leomachiavello/FundBio2024-2/Hardware/Diseño mecánico/planos_impresion.png

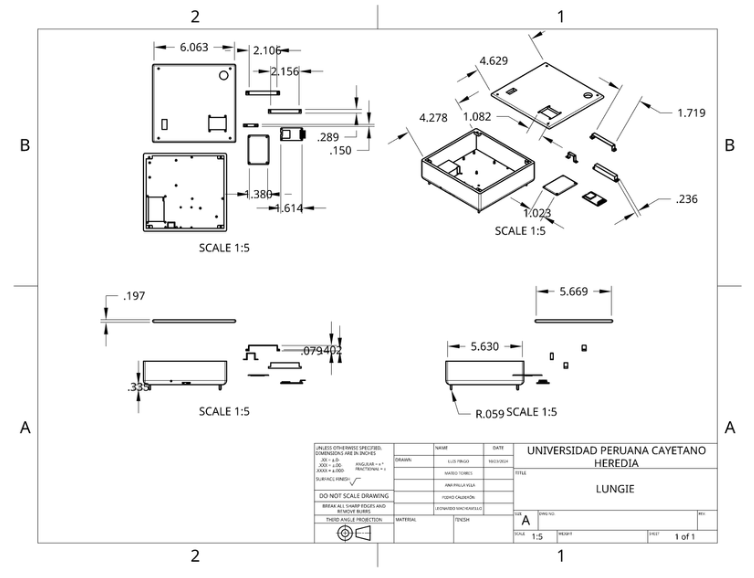
Hardware/Diseño mecánico/planos_impresion.png
