leomachiavello/FundBio2024-2/Imágenes/Espirometría_portátil.png

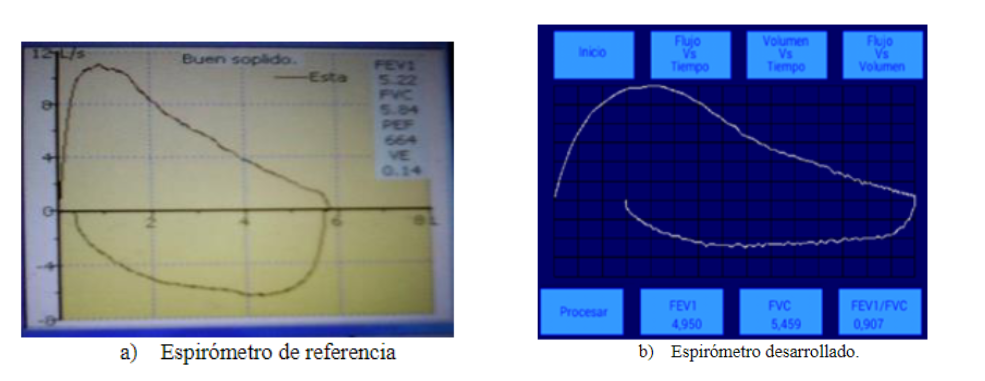
Imágenes/Espirometría_portátil.png
