leomachiavello/FundBio2024-2/Imágenes/espirómetro_asma.png

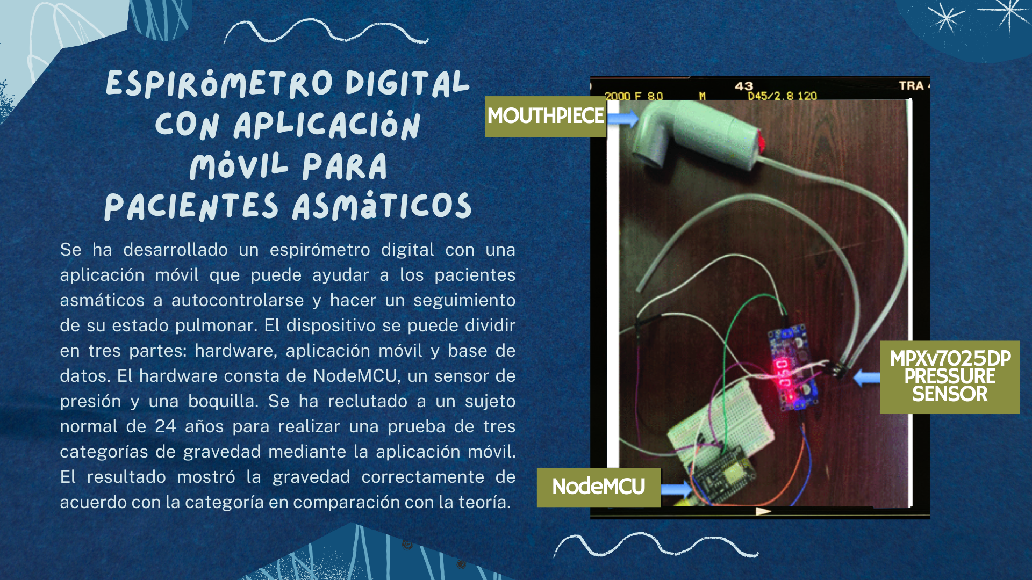
Imágenes/espirómetro_asma.png
