leomachiavello/FundBio2024-2/Imágenes/matriz.png

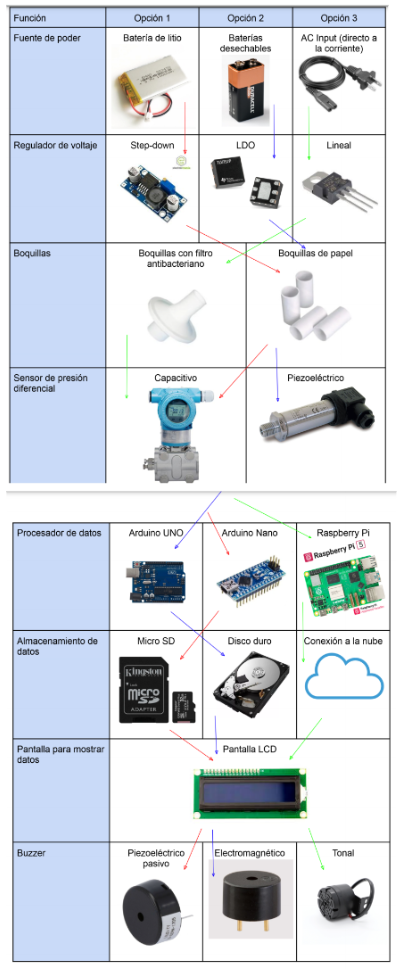
Imágenes/matriz.png
