leomachiavello/FundBio2024-2/Imágenes/matriz_2.png

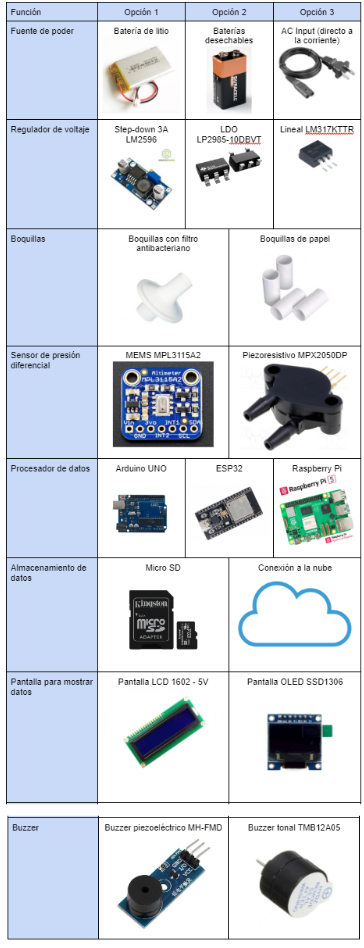
Imágenes/matriz_2.png
