leomachiavello/FundBio2024-2/Imágenes/matriz_3.png

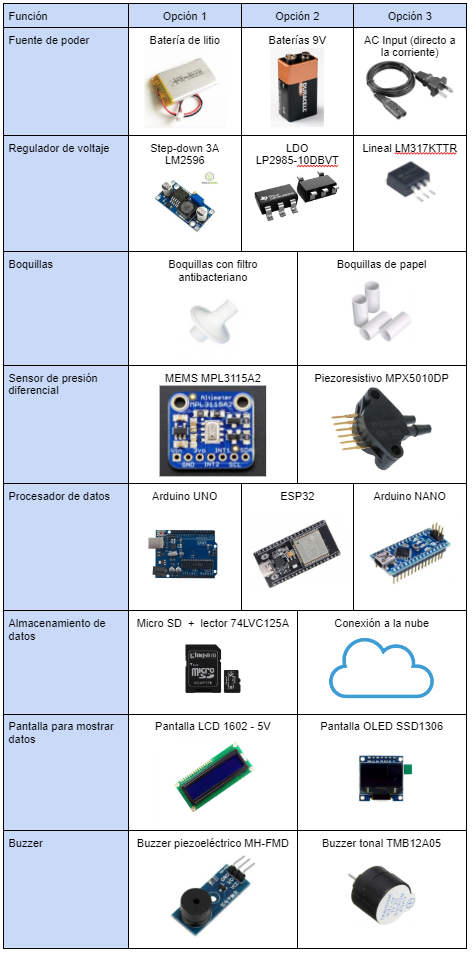
Imágenes/matriz_3.png
