leomachiavello/FundBio2024-2/Imágenes/matriz_4.png

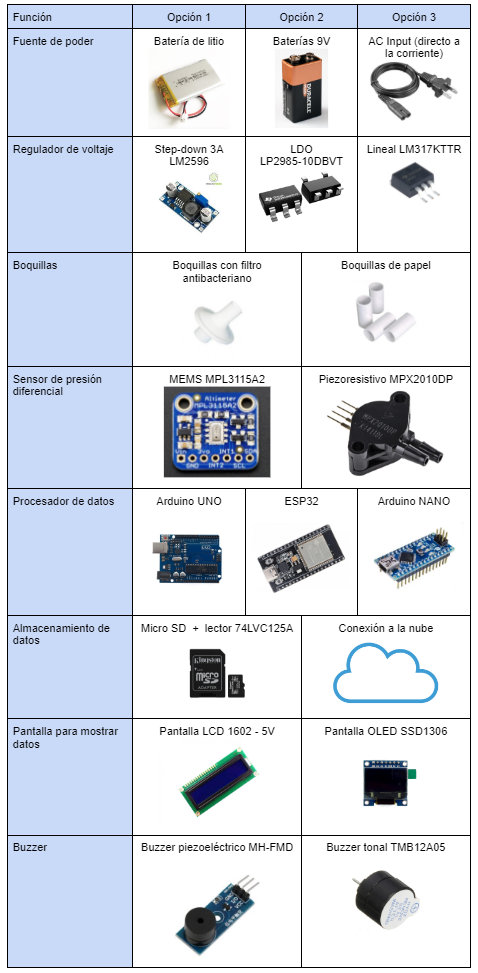
Imágenes/matriz_4.png
