leomachiavello/FundBio2024-2/Imágenes/propuesta_de_solucion.png

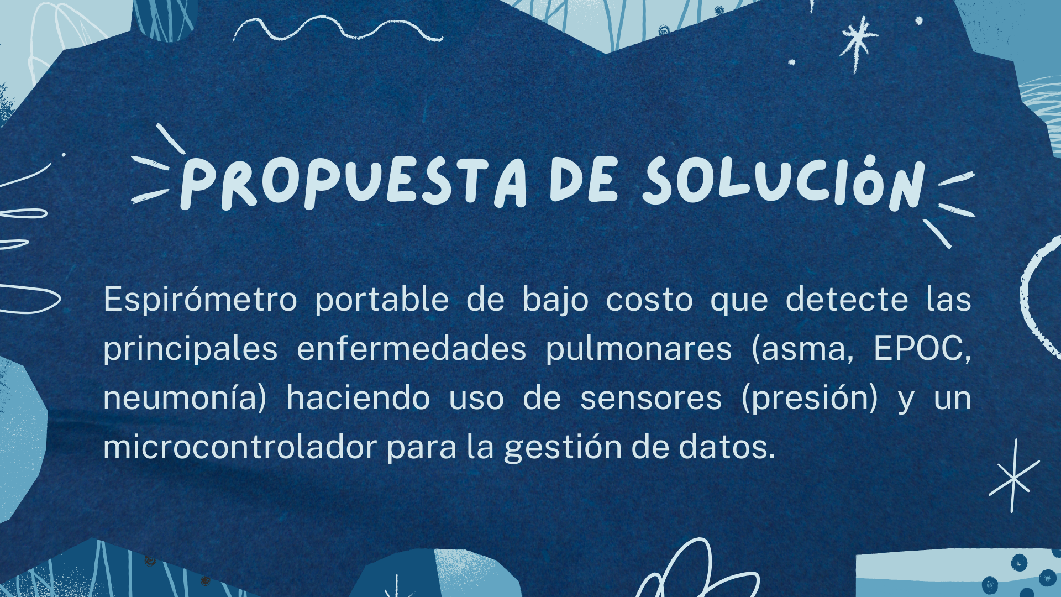
Imágenes/propuesta_de_solucion.png
