leomachiavello/FundBio2024-2/Imágenes/Schematic_FUNBIO_2024-10-08.png

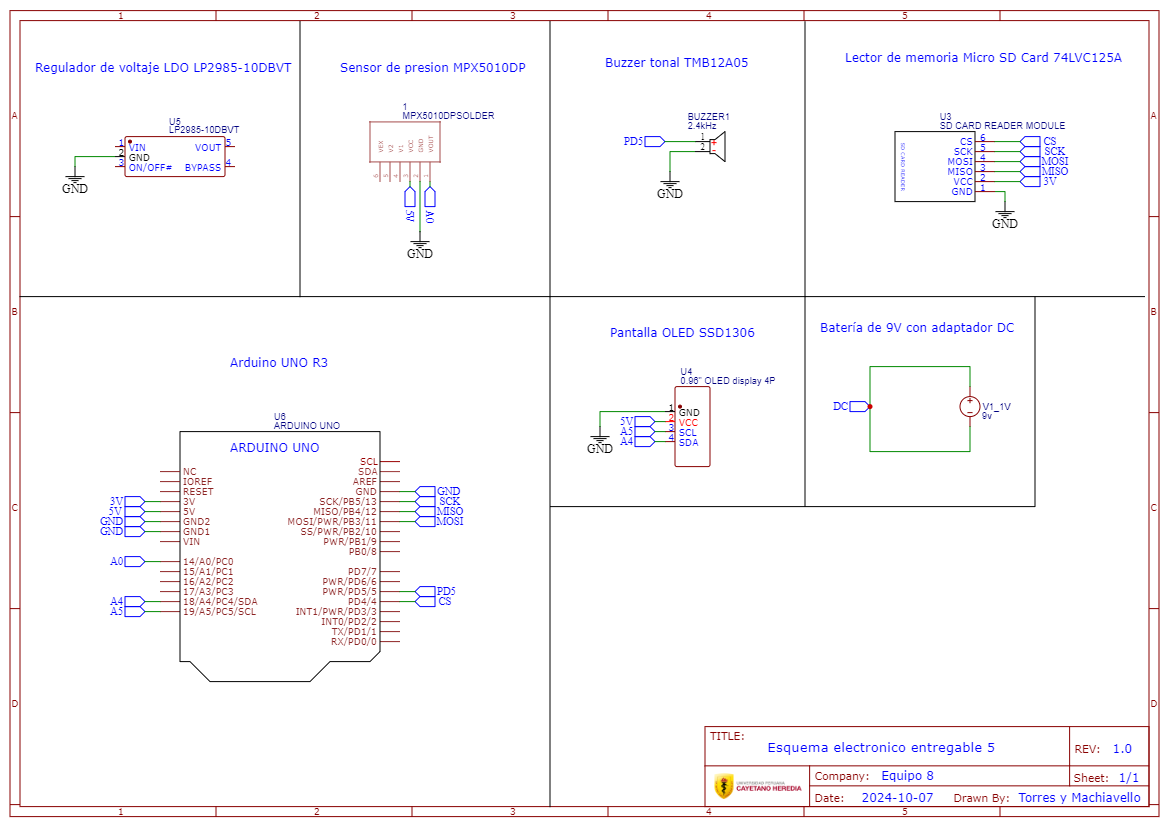
Imágenes/Schematic_FUNBIO_2024-10-08.png
