leomachiavello/FundBio2024-2/Imágenes/tabla_de_valoracion.png

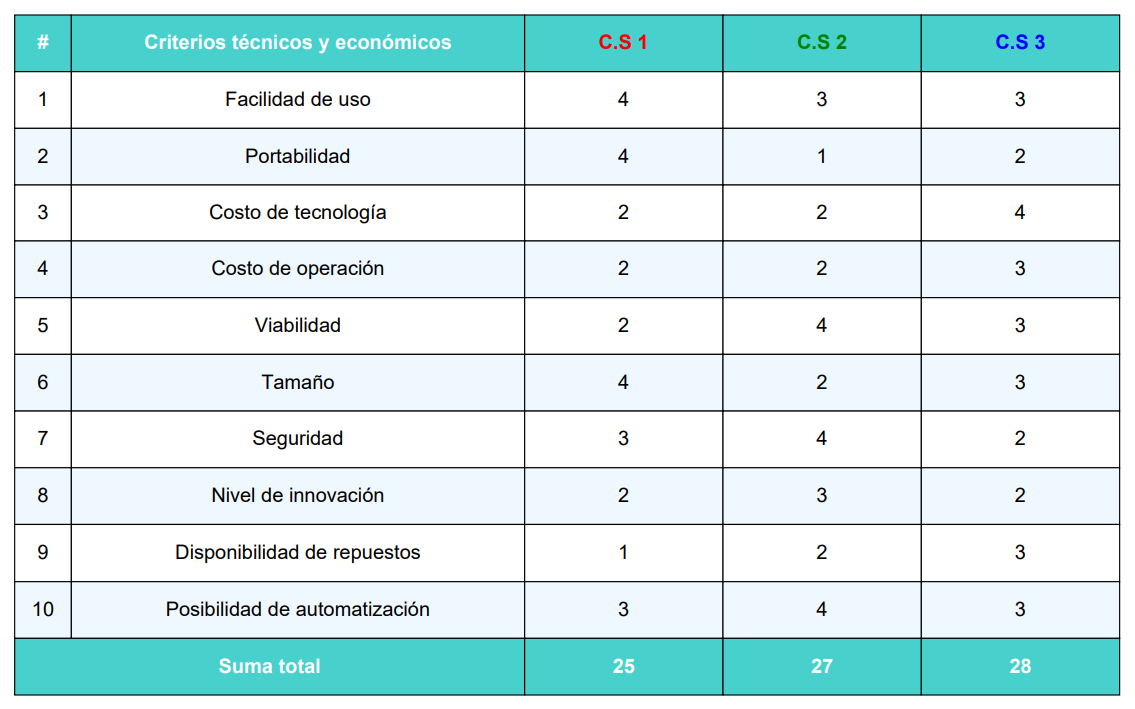
Imágenes/tabla_de_valoracion.png
