leomachiavello/FundBio2024-2/Imágenes/tabla_de_valoracion_2.png

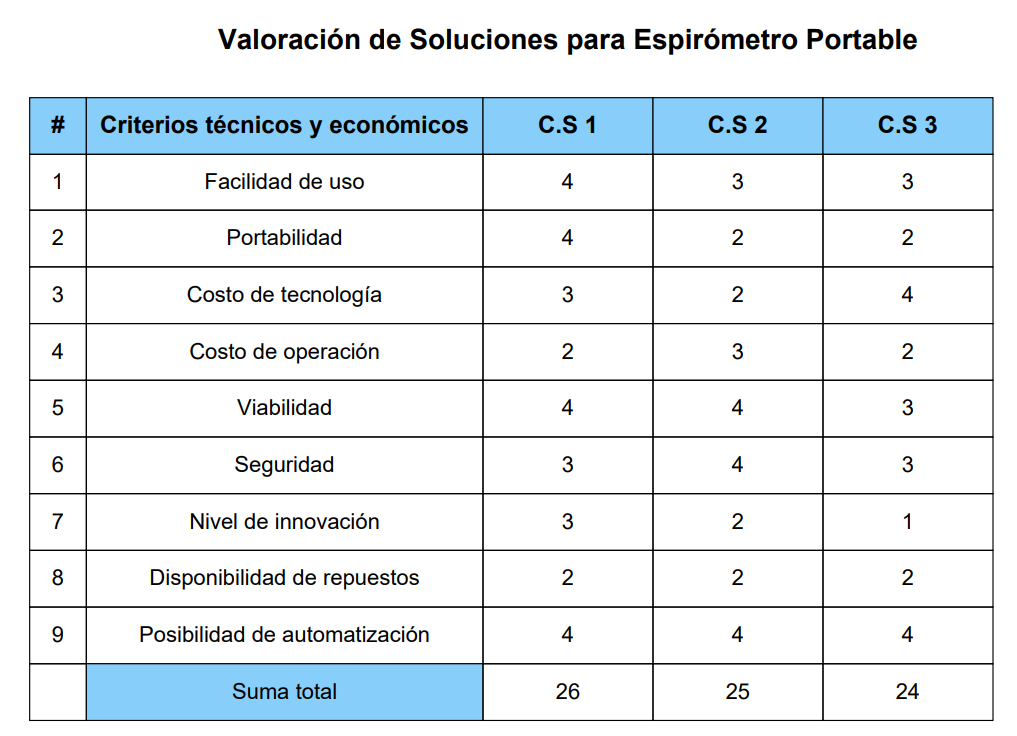
Imágenes/tabla_de_valoracion_2.png
