leomachiavello/FundBio2024-2/Imágenes/Tabla_requerimientos2.png

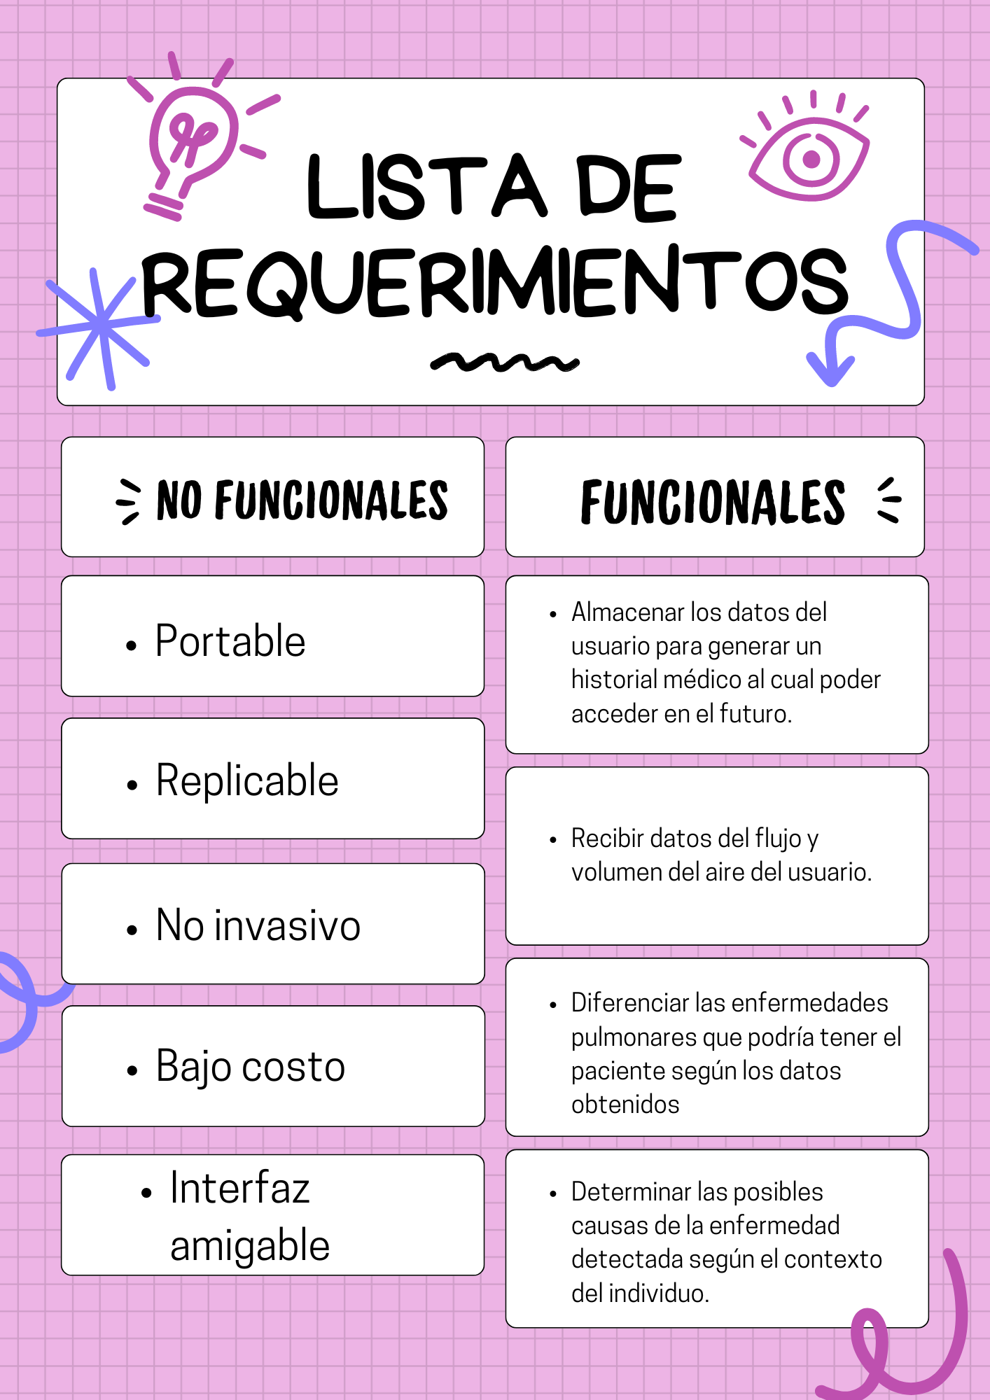
Imágenes/Tabla_requerimientos2.png
