leomachiavello/FundBio2024-2/Hardware/Diseño mecánico/Ensamblaje/Ensamblado_base.png

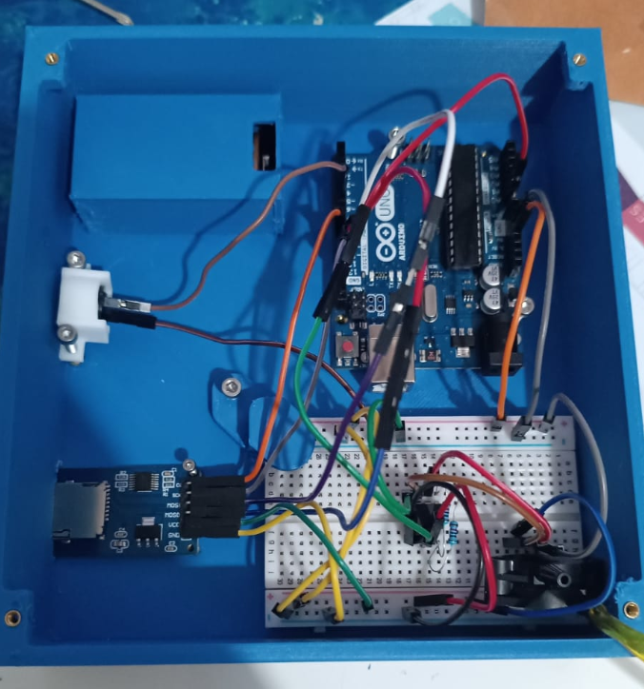
Hardware/Diseño mecánico/Ensamblaje/Ensamblado_base.png
