leomachiavello/FundBio2024-2/Hardware/Diseño mecánico/Ensamblaje/Ensamblado_tapa.png

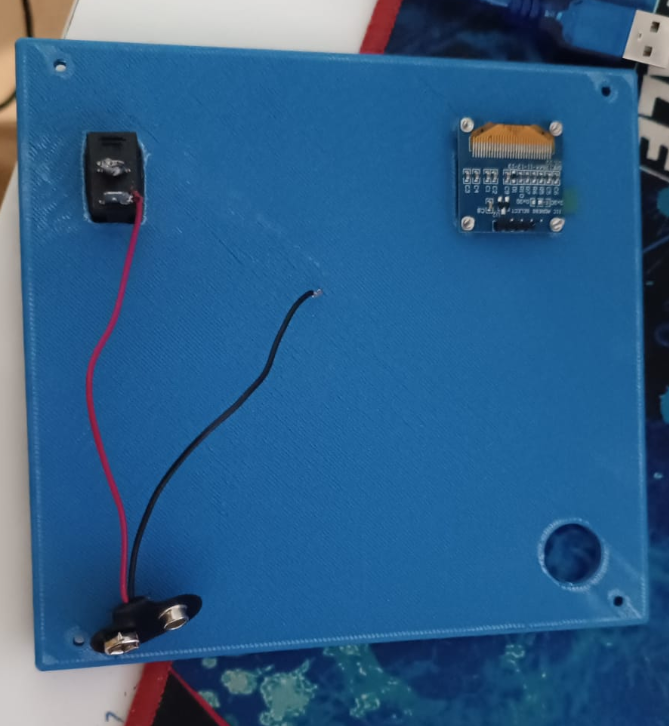
Hardware/Diseño mecánico/Ensamblaje/Ensamblado_tapa.png
