leomachiavello/FundBio2024-2/Hardware/Diseño mecánico/Planos borrador/Plano Soporte Buzzer.pdf

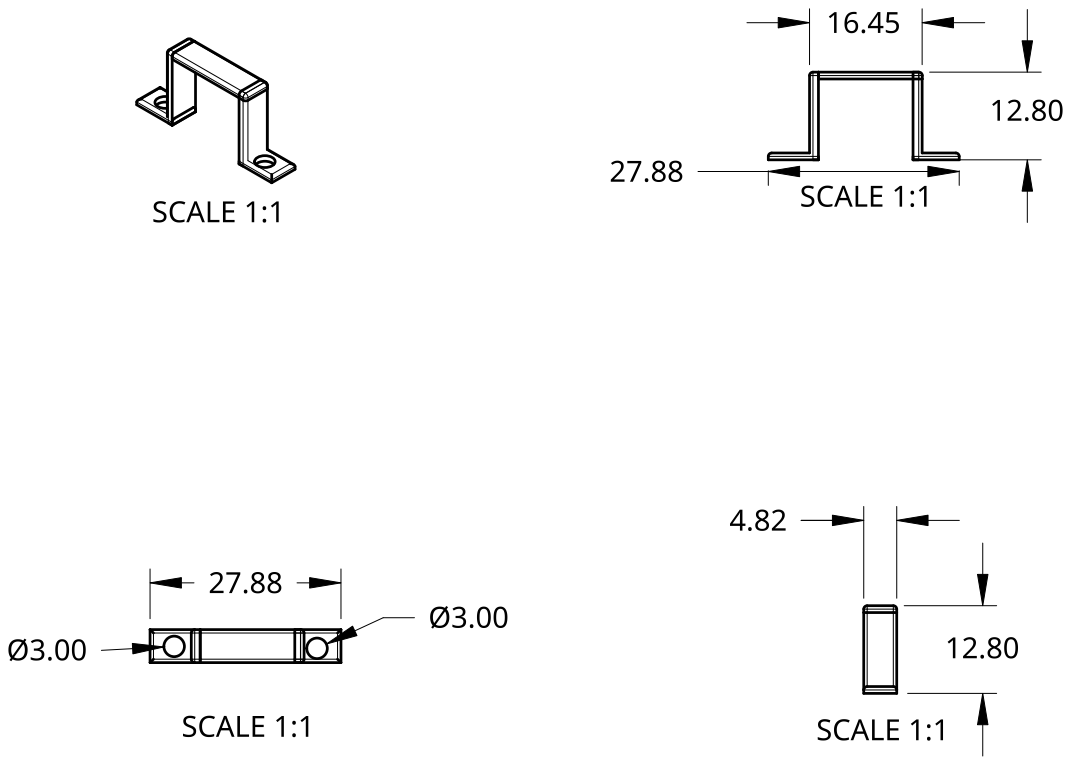
[picture p77: page 1]
