leomachiavello/FundBio2024-2/Hardware/Diseño mecánico/Planos borrador/Plano Soporte Protoboard Pared.pdf

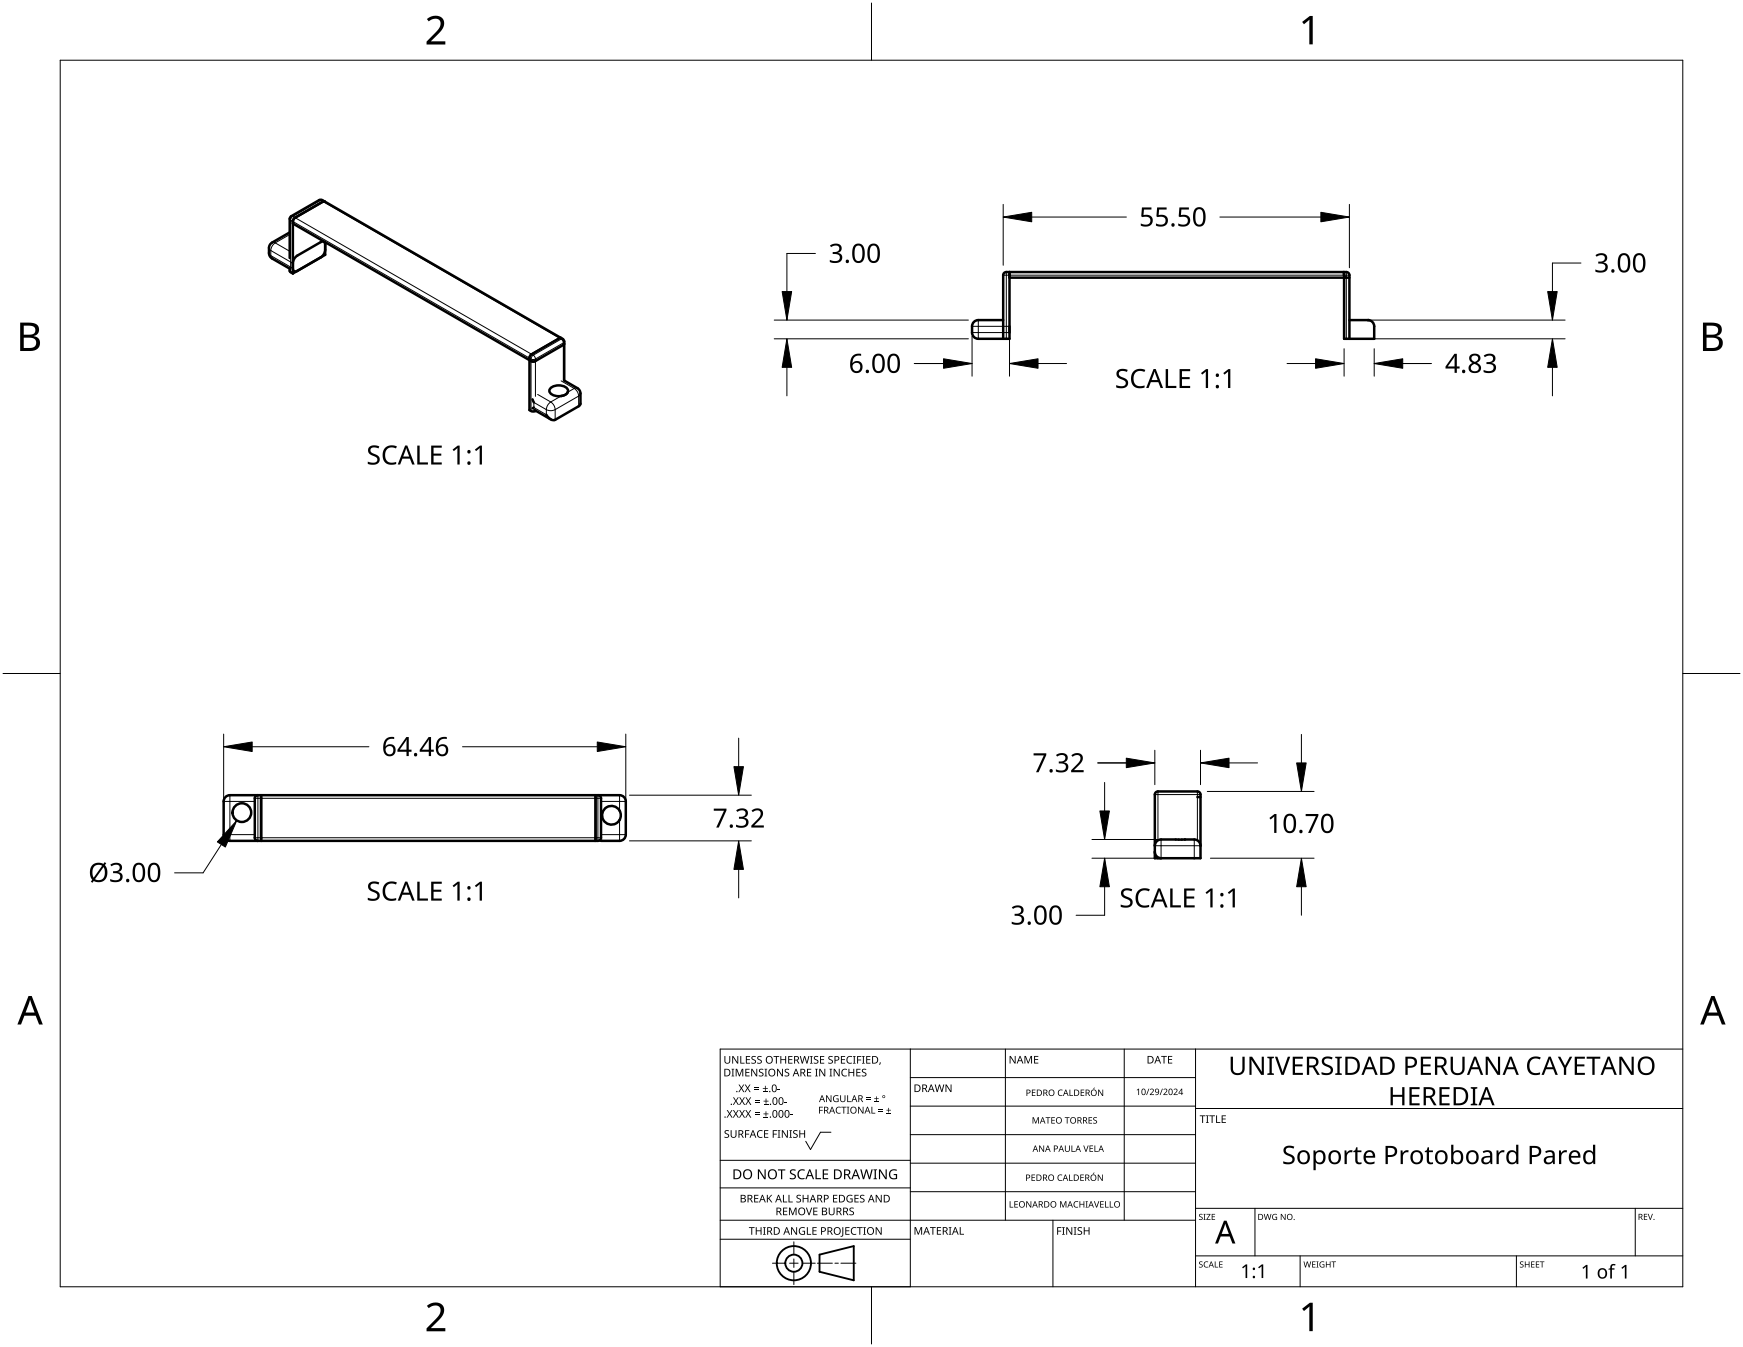
[picture p78: page 1]
