leomachiavello/FundBio2024-2/Hardware/Diseño mecánico/Planos borrador/Plano Soporte Protoboard.pdf

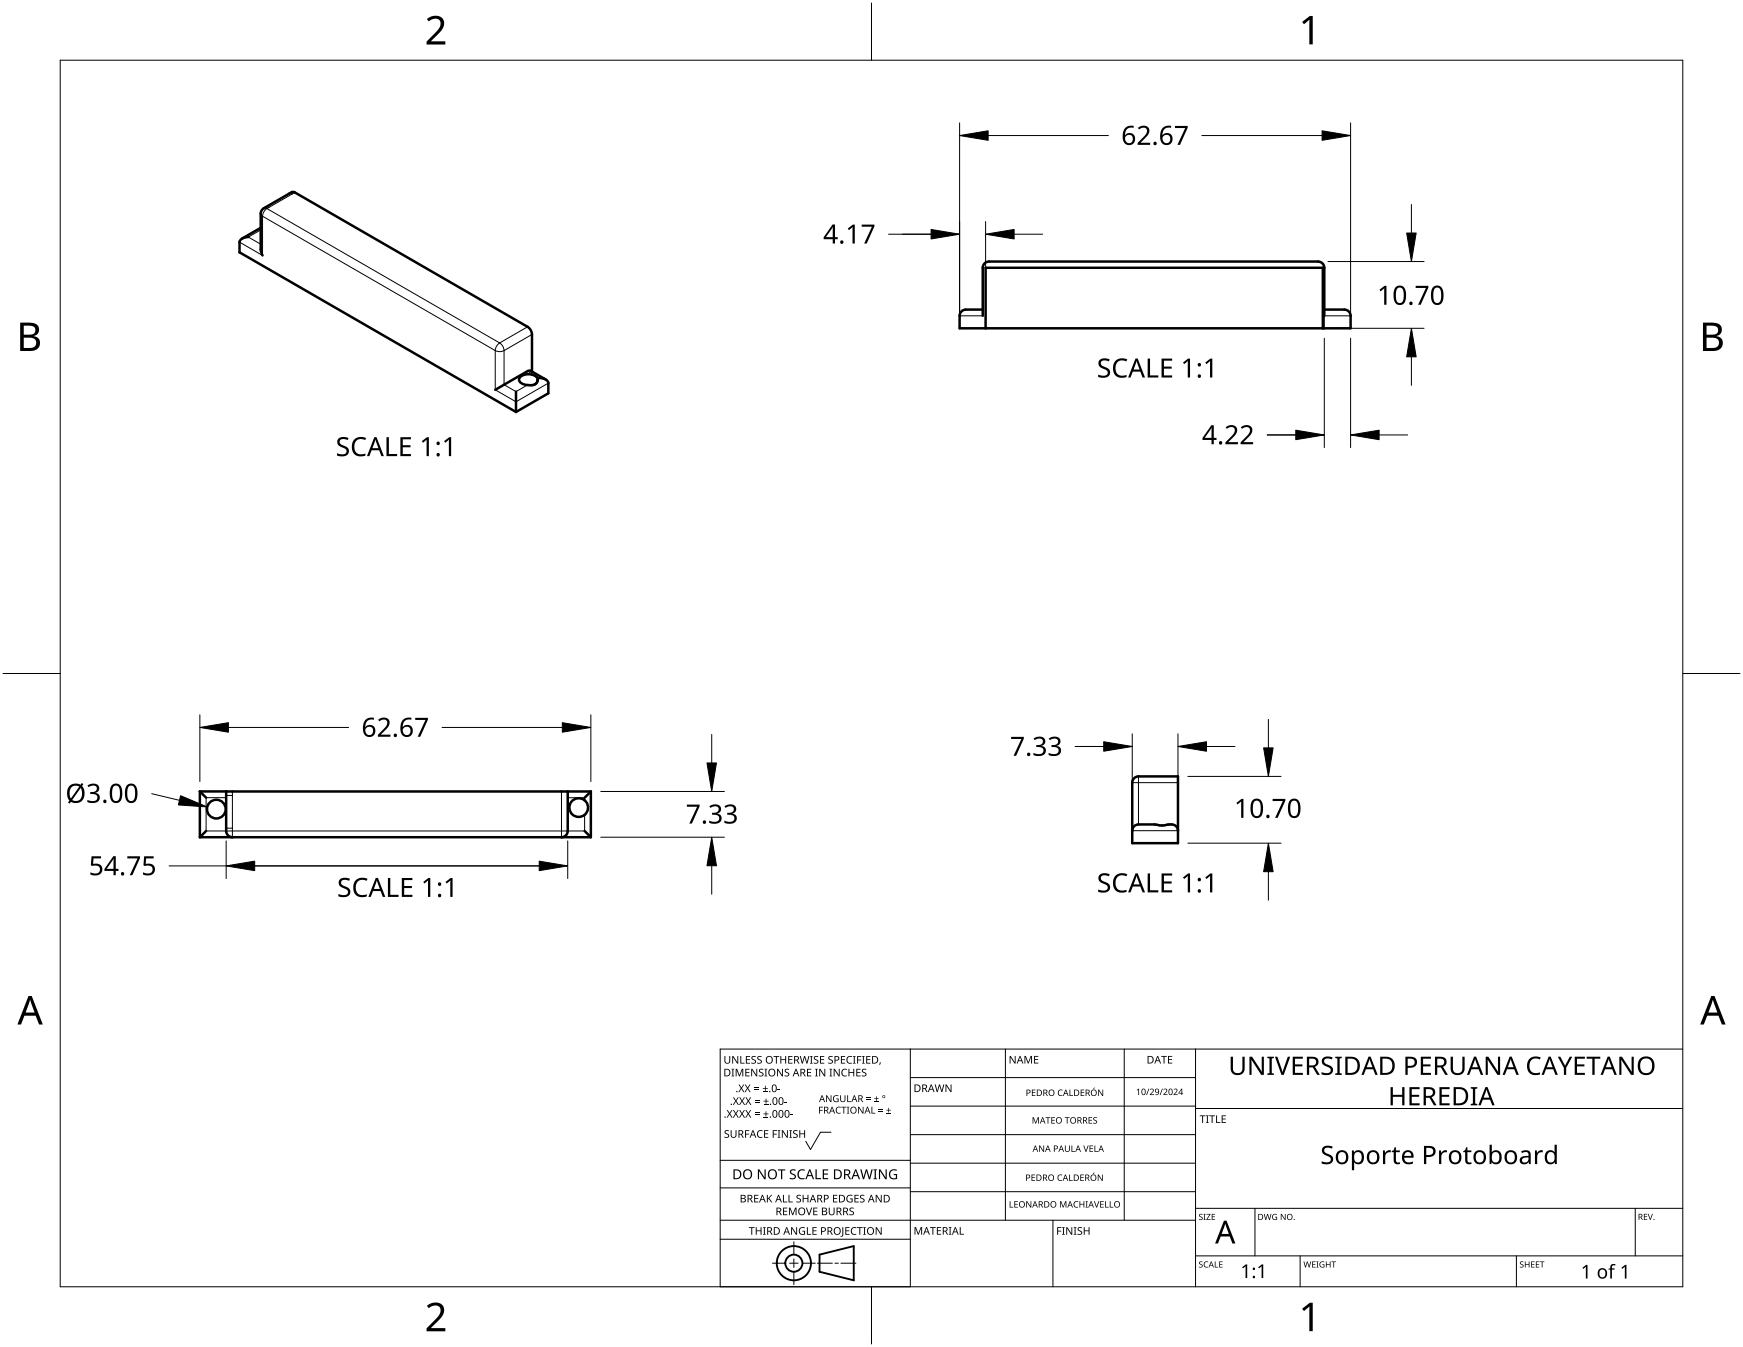
[picture p79: page 1]
