leomachiavello/FundBio2024-2/Hardware/Diseño mecánico/Planos borrador/Plano Tapa Bateria.pdf

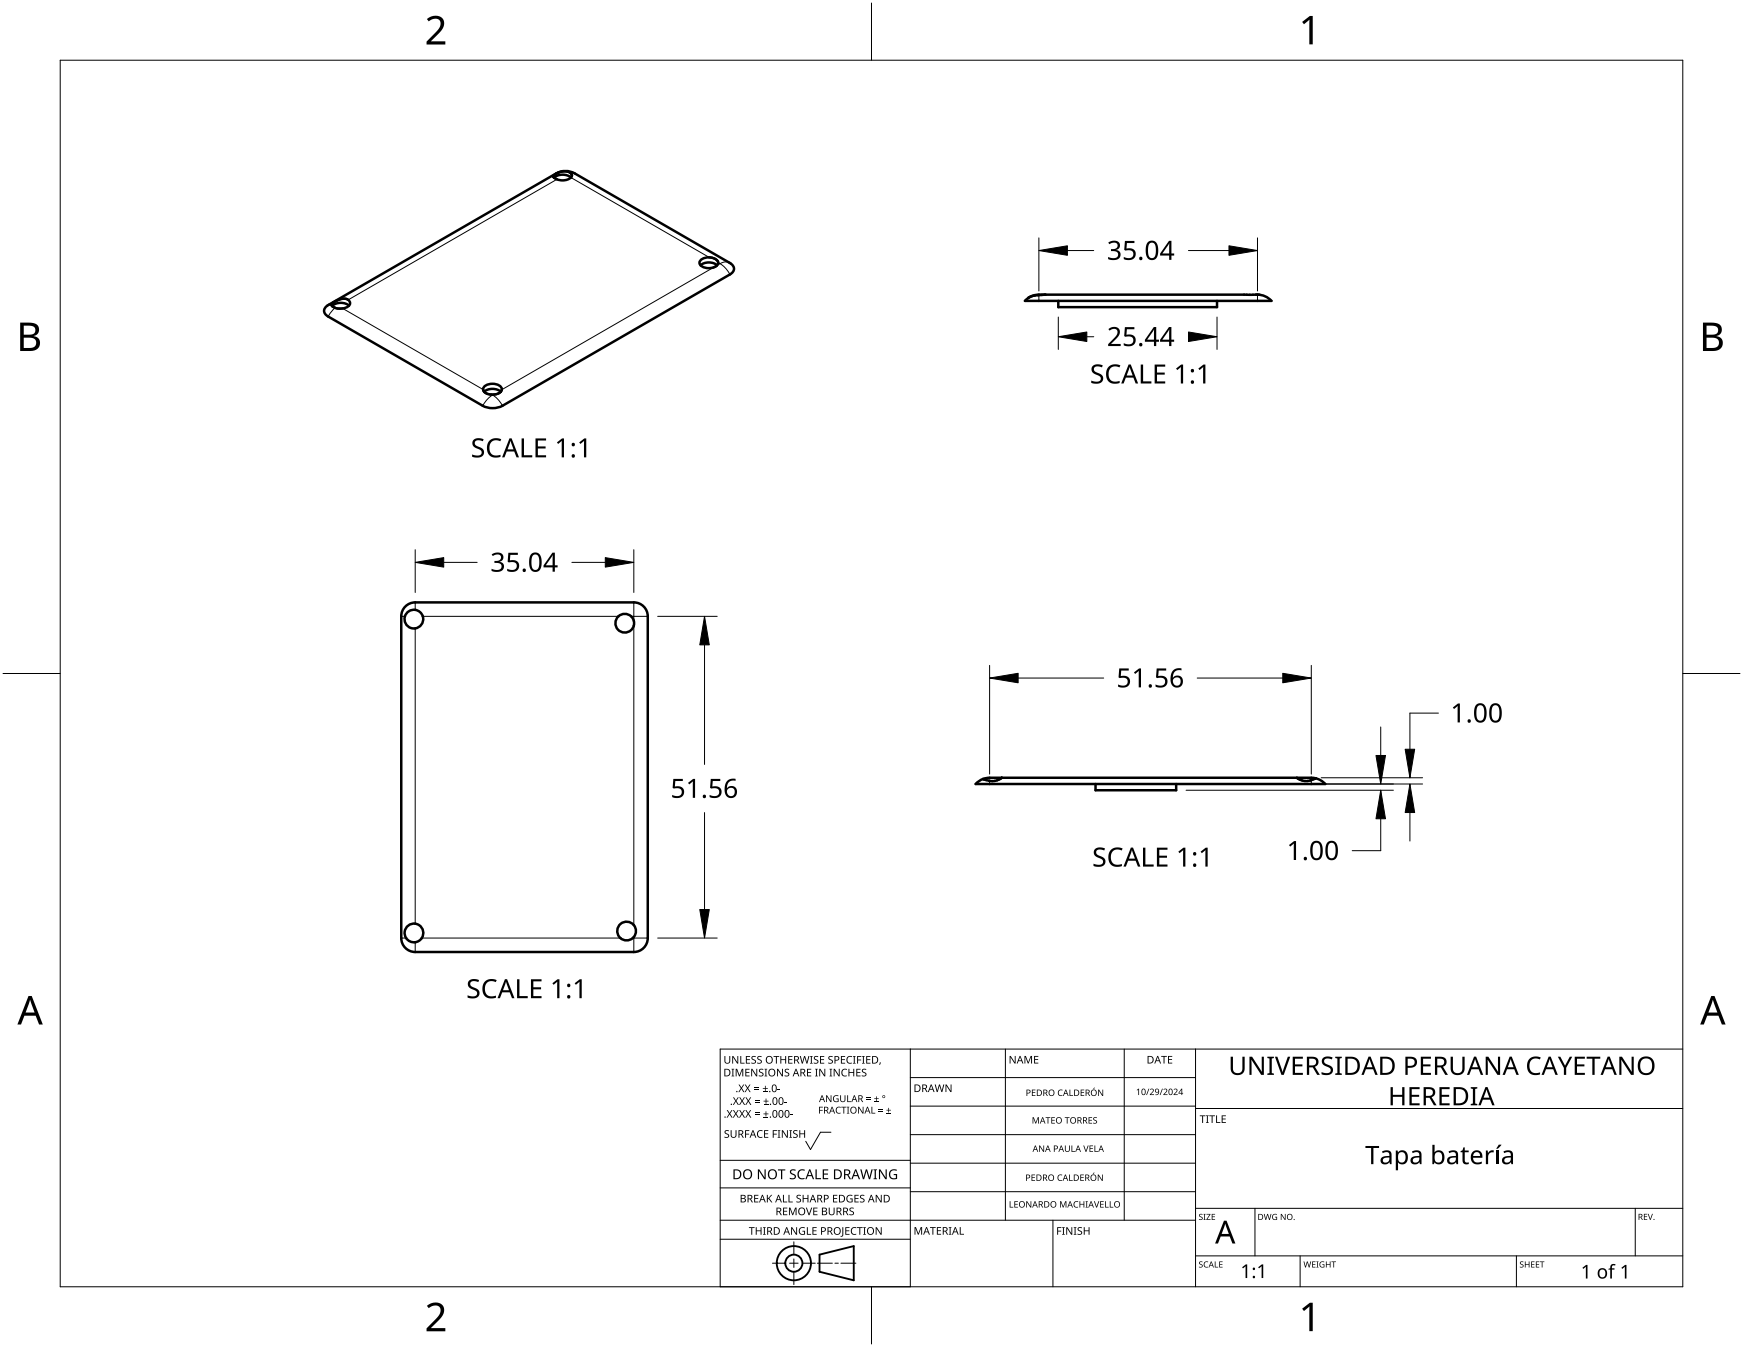
[picture p80: page 1]
