leomachiavello/FundBio2024-2/Hardware/Diseño mecánico/Planos borrador/Plano Tapa.pdf

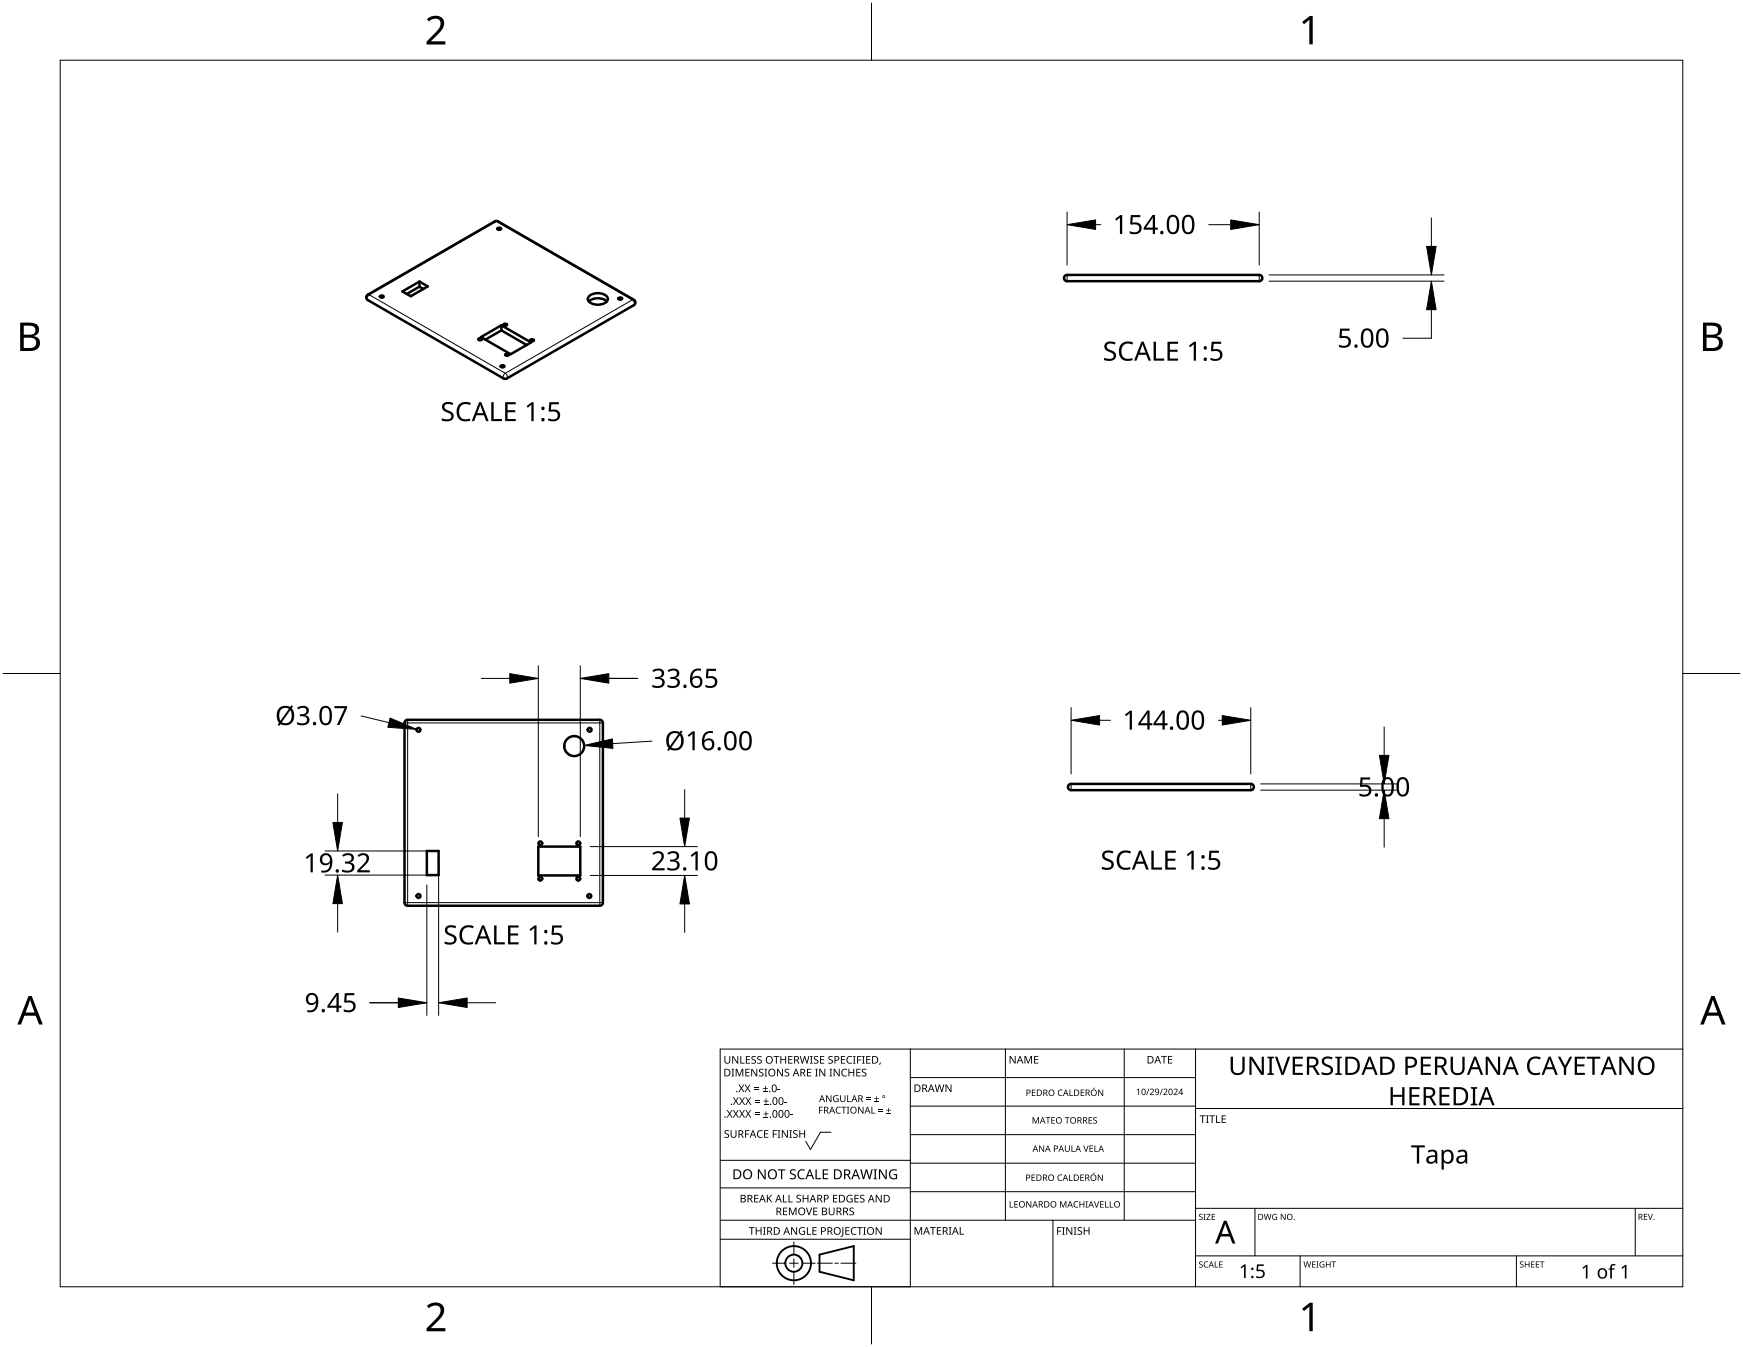
[picture p81: page 1]
